rszemeti/MicrowaveLocalOscillator/20230910_000221.jpg

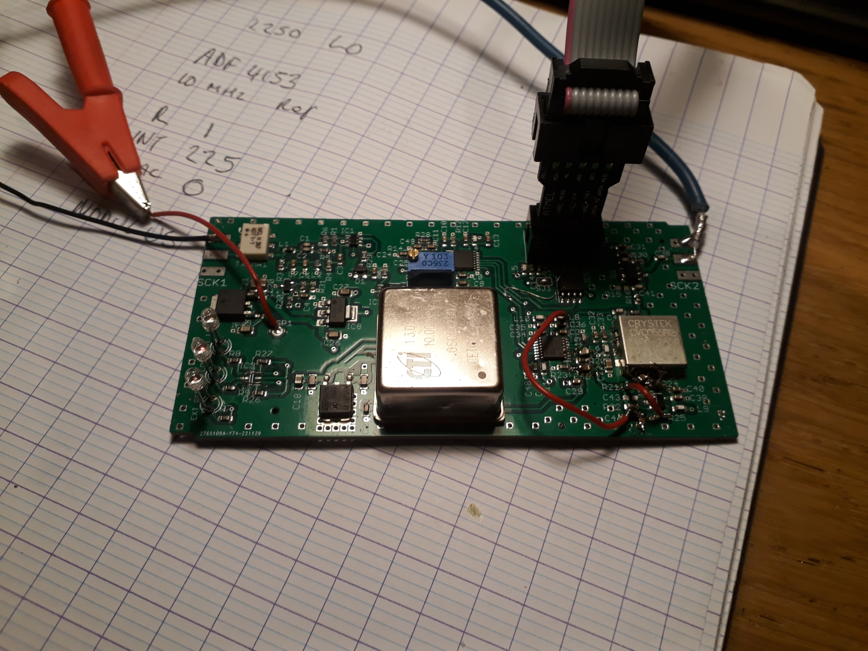
20230910_000221.jpg
