rszemeti/MicrowaveLocalOscillator/20230910_000301.jpg

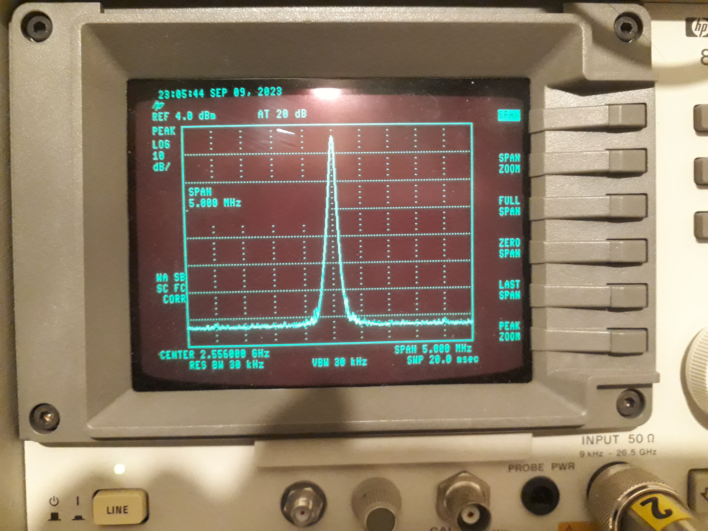
20230910_000301.jpg
