rszemeti/MicrowaveLocalOscillator/LoopFilter.asc

C1: cap; 22n
C2: cap; 220n
C3: cap; 1p
C4: cap; 1p
R1: res; 50R
R2: res; 150R
R3: res; 22k
R4: res; 39k
R5: res; 10k
R6: res; 18k
U1: opamp
V1: voltage; AC 1.
Named nets: 0
.ac oct 10 1 200000
.lib opamp.sub
