rszemeti/MicrowaveLocalOscillator/10MhzDiplexer.asc

C1: cap; 27p
C2: cap; 390p
C3: cap; 3.9p
C4: cap; 2700p
L1: ind; 82n
L2: ind; 8200n
R2: res; 50R
R3: res; 50R
R4: res; 50R
R5: res; 50R
V1: voltage; ""; AC 1.
Named nets: 0
.ac oct 30 900000 110000000
